mjc284/mjc284_homemade_motors/project_files/hardware/2-pole_AC/rotor_mount v3.stl

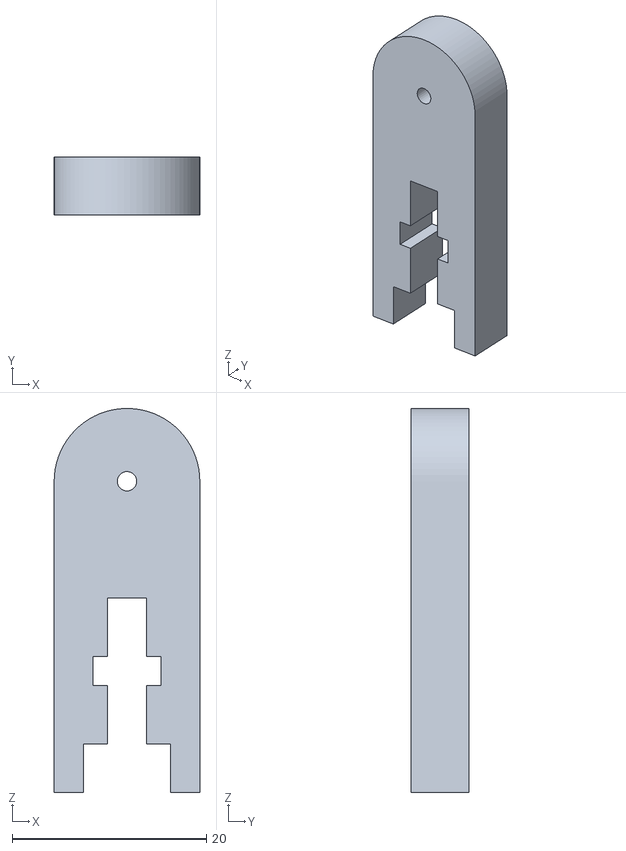
[picture p19: CAD file, 2022-10-03]
project_files/hardware/2-pole_AC/rotor_mount v3.stl
15.0 x 6.00 x 39.5
