mjc284/mjc284_homemade_motors/project_files/hardware/drill_DC/stand_R v3.stl

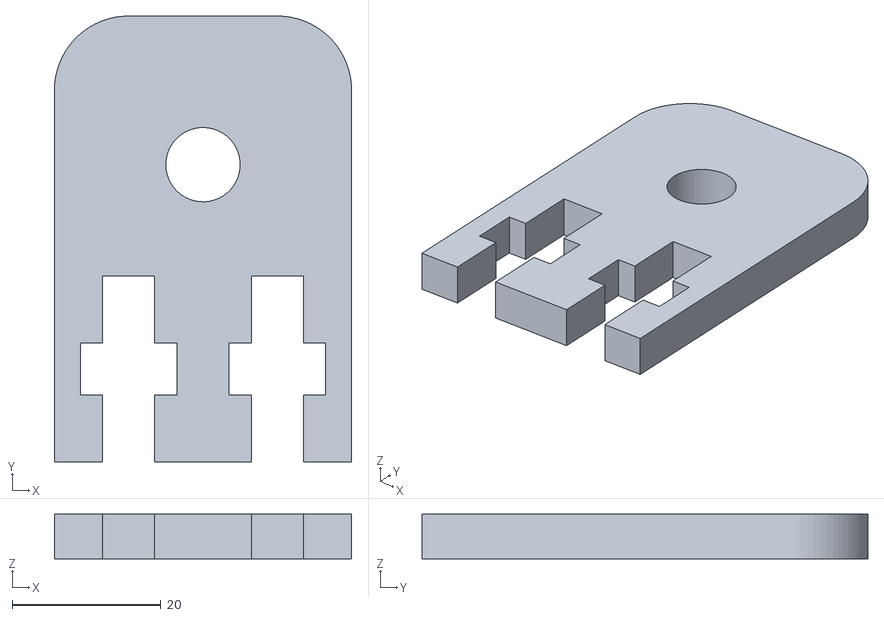
[picture p20: CAD file, 2022-10-03]
project_files/hardware/drill_DC/stand_R v3.stl
40.0 x 60.0 x 6.00
