mjc284/mjc284_homemade_motors/project_files/hardware/8-pole_AC/rotor_stand v6.stl

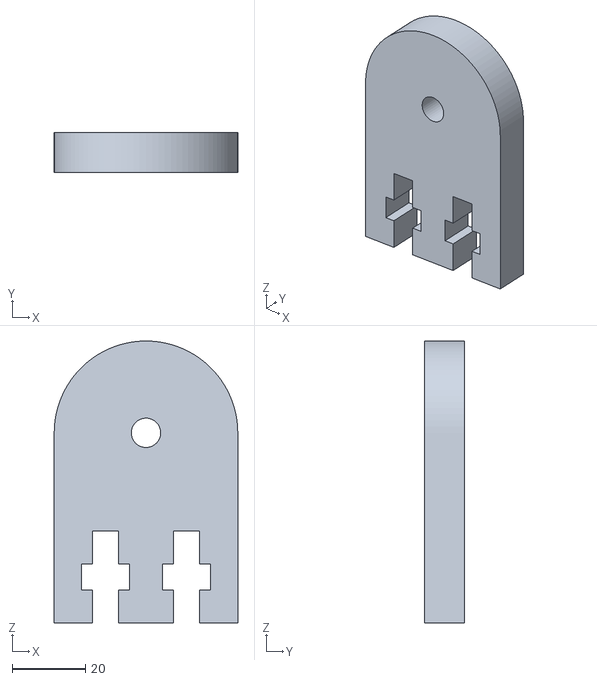
[picture p21: CAD file, 2022-10-03]
project_files/hardware/8-pole_AC/rotor_stand v6.stl
50.0 x 11.0 x 76.8
