mjc284/mjc284_homemade_motors/project_files/hardware/drill_DC/cap v4.stl

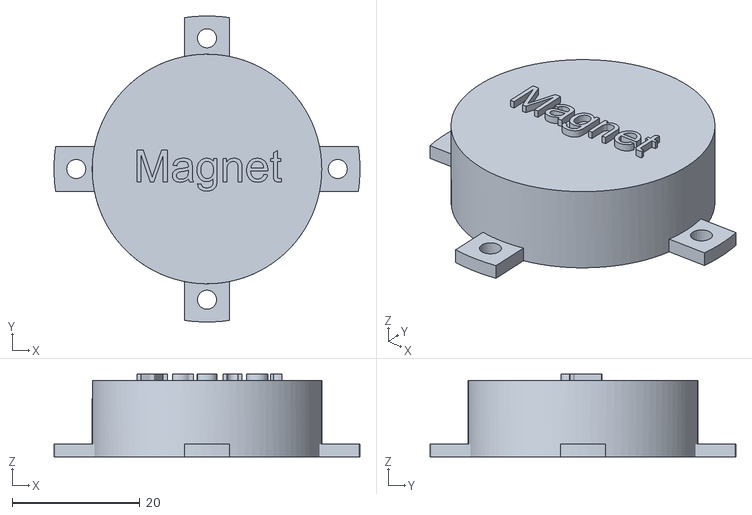
[picture p22: CAD file, 2022-10-03]
project_files/hardware/drill_DC/cap v4.stl
48.0 x 48.0 x 13.0
